luca-della-vedova/Teensynth/audio_interface/vs1053_plugins.h

// Plugins for VS1053B, taken from VLSI website

// Patches with various fixes
PROGMEM const uint16_t patches_plugin[]  = { /* Compressed plugin */
  0x0007,0x0001, /*copy 1*/
  0x8050,
  0x0006,0x001e, /*copy 30*/
  0x2a00,0xc000,0x3e12,0xb817,0x3e14,0xf812,0x3e01,0xb811,
  0x0007,0x9717,0x0020,0xffd2,0x0030,0x11d1,0x3111,0x8024,
  0x3704,0xc024,0x3b81,0x8024,0x3101,0x8024,0x3b81,0x8024,
  0x3f04,0xc024,0x2808,0x4800,0x36f1,0x9811,
  0x0007,0x0001, /*copy 1*/
  0x8060,
  0x0006,0x0510, /*copy 1296*/
  0xf400,0x4095,0x0000,0x02c2,0x6124,0x0024,0x0000,0x0024,
  0x2800,0x1ac5,0x4192,0x4542,0x0000,0x0041,0x2000,0x0015,
  0x0030,0x0317,0x2000,0x0000,0x3f00,0x4024,0x2000,0x0000,
  0x0000,0x0000,0x3e12,0x3800,0x3e00,0xb804,0x0030,0x0015,
  0x0007,0x8257,0x3700,0x984c,0xf224,0x1444,0xf224,0x0024,
  0x0008,0x0002,0x2910,0x0181,0x0000,0x1bc8,0xb428,0x1402,
  0x0000,0x8004,0x2910,0x0195,0x0000,0x1bc8,0xb428,0x0024,
  0x0006,0x0095,0x2800,0x2945,0x3e13,0x780e,0x3e11,0x7803,
  0x3e13,0xf806,0x3e11,0xf801,0x3510,0xb808,0x003f,0xe004,
  0xfec4,0x3800,0x48be,0x17c3,0xfec6,0x41c2,0x48be,0x4497,
  0x4090,0x1c46,0xf06c,0x0024,0x2400,0x2580,0x6090,0x41c3,
  0x6628,0x1c47,0x0000,0x0024,0x2800,0x2449,0xf07e,0x0024,
  0xf400,0x4182,0x673a,0x1c46,0x0000,0x0024,0x2800,0x2589,
  0xf06c,0x0024,0xf400,0x41c3,0x0000,0x0024,0x4224,0x3442,
  0x2902,0x1b40,0x4336,0x37c3,0x0000,0x1805,0x2902,0x1b40,
  0x4508,0x40c2,0x450a,0x9808,0x0000,0x0207,0xa478,0x1bc0,
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
  0x3400, 0x0007, 0x9255, 0x3d00, 0x0024, 0x0030, 0x0295, 0x6890, /*    8 */
  0x3400, 0x0030, 0x0495, 0x3d00, 0x0024, 0x2908, 0x4d40, 0x0030, /*   10 */
  0x0200, 0x000a, 0x0001, 0x0050,
#define MIDISTART_PLUGIN_SIZE 28
};
